kasunch/vlc-sync/digital/fpga/bench/dft-window-sync/idft_dft_tb.v

module idft_dft_tb();

    parameter WIDTH=10, FFT_SIZE=64, IDFT_OUTOUT_BLOCKS=4, DFT_SAMPLE_START_OFFSETS=128;

    reg clk, reset;
    
    integer i, j, k;
    integer f_idft_out;
    integer f_dft_out;
    
    reg [15:0] counter;
    
    reg r_idft_next;
    wire w_idft_next_out;
    reg signed [WIDTH-1:0] r_idft_in_real [FFT_SIZE-1:0];
    wire signed [WIDTH-1:0] w_idft_out_real [FFT_SIZE-1:0];
    reg [WIDTH-1:0] r_idft_out_real [FFT_SIZE*IDFT_OUTOUT_BLOCKS-1:0];
    
    reg r_dft_next;
    wire w_dft_next_out;
    reg signed [WIDTH-1:0] r_dft_in_real [FFT_SIZE-1:0];
    wire signed [WIDTH-1:0] w_dft_out_real [FFT_SIZE-1:0];
    wire signed [WIDTH-1:0] w_dft_out_imag [FFT_SIZE-1:0];

    idft_top idft_top_inst (.clk(clk), .reset(reset), .next(r_idft_next), .next_out(w_idft_next_out),
        // Assign only for the real parts of the input
        .X0(r_idft_in_real[0]), .X1(0),
        .X2(r_idft_in_real[1]), .X3(0),
        .X4(r_idft_in_real[2]), .X5(0),
        .X6(r_idft_in_real[3]), .X7(0),
        .X8(r_idft_in_real[4]), .X9(0),
        .X10(r_idft_in_real[5]), .X11(0),
        .X12(r_idft_in_real[6]), .X13(0),
        .X14(r_idft_in_real[7]), .X15(0),
        .X16(r_idft_in_real[8]), .X17(0),
        .X18(r_idft_in_real[9]), .X19(0),
        .X20(r_idft_in_real[10]), .X21(0),
        .X22(r_idft_in_real[11]), .X23(0),
        .X24(r_idft_in_real[12]), .X25(0),
        .X26(r_idft_in_real[13]), .X27(0),
        .X28(r_idft_in_real[14]), .X29(0),
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
        .Y94(w_dft_out_real[47]), .Y95(w_dft_out_imag[47]),
        .Y96(w_dft_out_real[48]), .Y97(w_dft_out_imag[48]),
        .Y98(w_dft_out_real[49]), .Y99(w_dft_out_imag[49]),
        .Y100(w_dft_out_real[50]), .Y101(w_dft_out_imag[50]),
        .Y102(w_dft_out_real[51]), .Y103(w_dft_out_imag[51]),
        .Y104(w_dft_out_real[52]), .Y105(w_dft_out_imag[52]),
        .Y106(w_dft_out_real[53]), .Y107(w_dft_out_imag[53]),
        .Y108(w_dft_out_real[54]), .Y109(w_dft_out_imag[54]),
        .Y110(w_dft_out_real[55]), .Y111(w_dft_out_imag[55]),
        .Y112(w_dft_out_real[56]), .Y113(w_dft_out_imag[56]),
        .Y114(w_dft_out_real[57]), .Y115(w_dft_out_imag[57]),
        .Y116(w_dft_out_real[58]), .Y117(w_dft_out_imag[58]),
        .Y118(w_dft_out_real[59]), .Y119(w_dft_out_imag[59]),
        .Y120(w_dft_out_real[60]), .Y121(w_dft_out_imag[60]),
        .Y122(w_dft_out_real[61]), .Y123(w_dft_out_imag[61]),
        .Y124(w_dft_out_real[62]), .Y125(w_dft_out_imag[62]),
        .Y126(w_dft_out_real[63]), .Y127(w_dft_out_imag[63]));        

       initial clk = 0;
       
       always #1 clk = ~clk;
       
       initial begin
       
          $dumpfile("idft_dft_tb.vcd");
          $dumpvars(0, idft_dft_tb);
          
          // We write the output of IDFT to this file
          f_idft_out = $fopen("output_idft_tb.csv");
          // We write the output of DFT to this file
          f_dft_out = $fopen("output_dft_tb.csv");
          
          for (i = 0; i < FFT_SIZE; i = i + 1) begin
              r_idft_in_real[i] <= 0;
              r_dft_in_real[i] <= 0;
          end
          
          r_idft_next <= 0;
          r_dft_next <= 0;
          reset <= 0;
          
          // Reset signal 
          @(posedge clk);
          reset <= 1;
          @(posedge clk);
          reset <= 0;
          
          @(posedge clk);
          
          
          for (j = 0; j < IDFT_OUTOUT_BLOCKS; j = j + 1) begin
              // Assert high to start IDFT
              r_idft_next <= 1;
              @(posedge clk);
              r_idft_next <= 0;
              
              // Start streaming input vector for IDFT
              // Create a Hermitian symmetry since we want a real valued signal
              r_idft_in_real[1] <= 25;
              r_idft_in_real[63] <= 25;

              r_idft_in_real[2] <= 25;
              r_idft_in_real[62] <= 25;
              
              r_idft_in_real[3] <= 25;
              r_idft_in_real[61] <= 25;
              
              r_idft_in_real[4] <= 25;
              r_idft_in_real[60] <= 25;
              
              // Wait until IDFT is done
              @(posedge w_idft_next_out);
              // IDFT module starts streaming output data at the next positive clock edge
              @(posedge clk);
              // We can read IDFT output at the next positive clock edge (registered access)
              @(posedge clk);
              // Print IDFT out to file
              for (i = 0; i < FFT_SIZE; i = i + 1) begin
                  $fwrite(f_idft_out, "%0d\n", (w_idft_out_real[i] ^ 10'h200));
                  r_idft_out_real[i + j * FFT_SIZE] <= w_idft_out_real[i] ^ 10'h200;
              end
          end
          
          
          for (j = 0; j < DFT_SAMPLE_START_OFFSETS; j = j + 1) begin
              // assert high to start DFT
              r_dft_next <= 1;
              @(posedge clk);
              r_dft_next <= 0;
              
              // Copy the real part of the IDFT output to the DFT input
              for (i = 0; i < FFT_SIZE; i = i + 1) begin
                  r_dft_in_real[i] <= r_idft_out_real[i + j] ^ 10'h200;
              end
              
              // Wait until DFT is done
              @(posedge w_dft_next_out);
              // DFT module starts streaming output data at the next positive clock edge
              @(posedge clk);
              // We can read DFT output at the next positive clock edge (registered access)
              @(posedge clk);

              for (i = 0; i < FFT_SIZE; i = i + 1) begin
                  $fwrite(f_dft_out, "%0d, %0d, ", w_dft_out_real[i], w_dft_out_imag[i]);
              end
              $fwrite(f_dft_out, "\n");

              @(posedge clk);
              @(posedge clk);
          end
          
          $fclose(f_idft_out);
          $fclose(f_dft_out);
          
          $finish;
          
       end

endmodule
