kasunch/vlc-sync/digital/fpga/bench/idft-dft/dft_tb.v

module dft_tb();

    reg clk, reset;
    
    integer i;
    
    reg [15:0] counter;
        
    reg r_dft_next;
    wire w_dft_next_out;
    reg signed [9:0] r_dft_in [127:0];
    wire signed [9:0] w_dft_out [127:0];
    
    // We load 128 samples to mem
    reg [9:0] mem [127:0];
    
    wire signed [9:0] DFT_IN0;
    wire signed [9:0] DFT_IN1;
    wire signed [9:0] DFT_IN2;
    wire signed [9:0] DFT_IN3;
    wire signed [9:0] DFT_IN4;
    wire signed [9:0] DFT_IN5;
    wire signed [9:0] DFT_IN6;
    wire signed [9:0] DFT_IN7;
    wire signed [9:0] DFT_IN8;
    wire signed [9:0] DFT_IN9;
    wire signed [9:0] DFT_IN10;
    wire signed [9:0] DFT_IN11;
    wire signed [9:0] DFT_IN12;
    wire signed [9:0] DFT_IN13;
    wire signed [9:0] DFT_IN14;
    wire signed [9:0] DFT_IN15;
    wire signed [9:0] DFT_IN16;
    wire signed [9:0] DFT_IN17;
    wire signed [9:0] DFT_IN18;
    wire signed [9:0] DFT_IN19;
    wire signed [9:0] DFT_IN20;
    wire signed [9:0] DFT_IN21;
    wire signed [9:0] DFT_IN22;
    wire signed [9:0] DFT_IN23;
    wire signed [9:0] DFT_IN24;
    wire signed [9:0] DFT_IN25;
    wire signed [9:0] DFT_IN26;
    wire signed [9:0] DFT_IN27;
    wire signed [9:0] DFT_IN28;
    wire signed [9:0] DFT_IN29;
    wire signed [9:0] DFT_IN30;
    wire signed [9:0] DFT_IN31;
    wire signed [9:0] DFT_IN32;
    wire signed [9:0] DFT_IN33;
    wire signed [9:0] DFT_IN34;
    wire signed [9:0] DFT_IN35;
    wire signed [9:0] DFT_IN36;
    wire signed [9:0] DFT_IN37;
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
    cmplx_to_mag cmpx_mag_inst61 (.i_i(DFT_OUT122), .i_q(DFT_OUT123), .o_mag(DFT_OUT_MAG61));
    cmplx_to_mag cmpx_mag_inst62 (.i_i(DFT_OUT124), .i_q(DFT_OUT125), .o_mag(DFT_OUT_MAG62));
    cmplx_to_mag cmpx_mag_inst63 (.i_i(DFT_OUT126), .i_q(DFT_OUT127), .o_mag(DFT_OUT_MAG63));

       initial clk = 0;
       
       always #1 clk = ~clk;
       
       initial begin
       
          $dumpfile("dft_tb.vcd");
          $dumpvars(0, dft_tb);
          
          // The input_dft_tb.hex file has 128 samples (10-bit) captured from an ADC
          $readmemh("input_dft_tb.hex", mem);
          
          for (i = 0; i < 128; i = i + 1) begin
              r_dft_in[i] <= 0;
          end
          
          r_dft_next <= 0;
          reset <= 0;
          
          // Reset signal 
          @(posedge clk);
          reset <= 1;
          @(posedge clk);
          reset <= 0;
          
          @(posedge clk);
                    
          // assert high to start DFT
          r_dft_next <= 1;
          @(posedge clk);
          r_dft_next <= 0;
          
          // Copy first 64 samples to the real input of the DFT
          for (i = 0; i < 64; i = i + 1) begin
              // We have to convet the unsigned samples to signed values
              r_dft_in[i*2] <= mem[i] ^ 10'h200;
          end
          
          // Wait until DFT is done
          @(posedge w_dft_next_out);
          // DFT module starts streaming output data at the next positive clock edge
          @(posedge clk);
          // We can read DFT output at the next positive clock edge (registered access)
          @(posedge clk);
          for (i = 0; i < 64; i = i + 1) begin
              $display("%d, %d", w_dft_out[i*2], w_dft_out[i*2+1]);
          end

          // Wait two more clock cycles so, we can see the output in the simulator
          @(posedge clk);
          @(posedge clk);
          
          $finish;
          
       end

endmodule
