kasunch/vlc-sync/digital/fpga/bench/idft-dft/idft_dft_tb.v

module idft_dft_tb();

    reg clk, reset;
    
    integer i;
    
    reg [15:0] counter;
    
    reg r_idft_next;
    wire w_idft_next_out;
    reg [9:0] r_idft_in [127:0];
    wire [9:0] w_idft_in [127:0];
    wire [9:0] w_idft_out [127:0];
    
    reg r_dft_next;
    wire w_dft_next;
    wire w_dft_next_out;
    reg [9:0] r_dft_in [127:0];
    wire [9:0] w_dft_in [127:0];
    wire [9:0] w_dft_out [127:0];

    wire [9:0] IDFT_IN0;
    wire [9:0] IDFT_IN1;
    wire [9:0] IDFT_IN2;
    wire [9:0] IDFT_IN3;
    wire [9:0] IDFT_IN4;
    wire [9:0] IDFT_IN5;
    wire [9:0] IDFT_IN6;
    wire [9:0] IDFT_IN7;
    wire [9:0] IDFT_IN8;
    wire [9:0] IDFT_IN9;
    wire [9:0] IDFT_IN10;
    wire [9:0] IDFT_IN11;
    wire [9:0] IDFT_IN12;
    wire [9:0] IDFT_IN13;
    wire [9:0] IDFT_IN14;
    wire [9:0] IDFT_IN15;
    wire [9:0] IDFT_IN16;
    wire [9:0] IDFT_IN17;
    wire [9:0] IDFT_IN18;
    wire [9:0] IDFT_IN19;
    wire [9:0] IDFT_IN20;
    wire [9:0] IDFT_IN21;
    wire [9:0] IDFT_IN22;
    wire [9:0] IDFT_IN23;
    wire [9:0] IDFT_IN24;
    wire [9:0] IDFT_IN25;
    wire [9:0] IDFT_IN26;
    wire [9:0] IDFT_IN27;
    wire [9:0] IDFT_IN28;
    wire [9:0] IDFT_IN29;
    wire [9:0] IDFT_IN30;
    wire [9:0] IDFT_IN31;
    wire [9:0] IDFT_IN32;
    wire [9:0] IDFT_IN33;
    wire [9:0] IDFT_IN34;
    wire [9:0] IDFT_IN35;
    wire [9:0] IDFT_IN36;
    wire [9:0] IDFT_IN37;
    wire [9:0] IDFT_IN38;
    wire [9:0] IDFT_IN39;
    wire [9:0] IDFT_IN40;
    wire [9:0] IDFT_IN41;
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
      .X122(DFT_IN122), .Y122(DFT_OUT122),
      .X123(DFT_IN123), .Y123(DFT_OUT123),
      .X124(DFT_IN124), .Y124(DFT_OUT124),
      .X125(DFT_IN125), .Y125(DFT_OUT125),
      .X126(DFT_IN126), .Y126(DFT_OUT126),
      .X127(DFT_IN127), .Y127(DFT_OUT127));


       initial clk = 0;
       
       always #1 clk = ~clk;
       
       initial begin
       
          $dumpfile("idft_dft_tb.vcd");
          $dumpvars(0, idft_dft_tb);
          
          for (i = 0; i < 128; i = i + 1) begin
              r_idft_in[i] <= 0;
              r_dft_in[i] <= 0;
          end
          
          r_idft_next <= 0;
          r_dft_next <= 0;
          reset <= 0;
          
          // Reset signal 
          @(posedge clk);
          reset <= 1;
          @(posedge clk);
          reset <= 0;
          
          @(posedge clk);
          
          // Assert high to start IDFT
          r_idft_next <= 1;
          @(posedge clk);
          r_idft_next <= 0;
          
          // Start streaming input vector for IDFT
          // Create a Hermitian symmetry
          r_idft_in[20] <= 25;
          
          r_idft_in[108] <= 25;
          
          // Wait until IDFT is done
          @(posedge w_idft_next_out);
          // IDFT module starts streaming output data at the next positive clock edge
          @(posedge clk);
          // We can read IDFT output at the next positive clock edge (registered access)
          @(posedge clk);
          // Print IDFT out
          $display("----------------------------");
          for (i = 0; i < 64; i = i + 1) begin
              $display("IDFT_OUT%03d = %x, %x", i, w_idft_out[i*2], w_idft_out[i*2+1]);
          end
          
          // assert high to start DFT
          r_dft_next <= 1;
          @(posedge clk);
          r_dft_next <= 0;
          
          // Copy the real part of the IDFT output to the DFT input
          for (i = 0; i < 128; i = i + 2) begin
              r_dft_in[i] <= w_idft_out[i];
          end
          
          // Wait until DFT is done
          @(posedge w_dft_next_out);
          // DFT module starts streaming output data at the next positive clock edge
          @(posedge clk);
          // We can read DFT output at the next positive clock edge (registered access)
          @(posedge clk);
          // Print DFT out
          $display("----------------------------");
          for (i = 0; i < 64; i = i + 1) begin
              $display("DFT_OUT%03d = %x, %x", i, w_dft_out[i*2], w_dft_out[i*2+1]);
          end

          
          @(posedge clk);
          @(posedge clk);
          
          $finish;
          
       end

endmodule
